telefab/POV3DLED/Globe/BusParams.h

/**
 * Parameters of the bus. All times in us.
 * These delays are long because the receiving Arduino is overloaded, which reduces its ccuracy.
 */

/**
 * Duration of a pulse
 */
#define BUS_PULSE 10

/**
 * Basic duration of a symbol, multiplied for each different symbol
 */
#define BUS_SYMBOL_BASE 100

/**
 * Number of times a byte should be repeated
 */
#define BUS_BYTE_REPEAT 3

/**
 * Number of bits used to indicate 
 * the position in the flow of the current byte
 */
 #define BUS_BYTE_INDEX_BITS 2

/**
 * Symbol: end of message
 */
#define BUS_SYM_END 2

/**
 * Size (in bytes) of the buffer to store data when receiving
 */
#define BUS_FIFO_SIZE 20
