telefab/POV3DLED/Globe/examples/DrawSender/WebRequest.h

/*
 * Represents an HTTP request
 */

#include <Arduino.h>
#include <Ethernet.h>

// Request parsing state indicators
typedef enum {
  SERV_REQ_METHOD,
  SERV_REQ_RESOURCE,
  SERV_REQ_PARAMS,
  SERV_REQ_EMPTY_LINE,
  SERV_REQ_MISC,
  SERV_REQ_REPLIED
} WebRequestState;

class WebRequest {

  private:
    // Client handle to receive the body if needed
    EthernetClient* client;
  public:
    // State of the processing of the request
    WebRequestState state;
    // Data received in the request
    String method, resource, params;
    
    /**
     * Initial empty request constructor
     */
    WebRequest():
      client(NULL),
      state(SERV_REQ_METHOD)
    {
    }
    
    /**
     * Clear request data (new request)
     */
    void clear(EthernetClient* client);

    /**
     * Returns if a body character is available
     */
    bool bodyAvailable();

    /**
     * Returns a body character if available
     */
    char bodyRead();
};
